marcobrianza/WeMakeColorsII/Arduino/WeMakeColorsII/app_status.h

#include "LED.h"

int const APP_START = 0;
int const UPDATE = 1;
int const AUTO_UPDATE = 2;
int const UPDATE_ERROR = -3;
int const UPDATE_OK = 3;
int const WIFI_MANAGER_AP = 4;
int const WIFI_MANAGER_SAVE = 5;


void showState(int s) {
  rgbColor_t c;
  //String ss;
  switch (s) {
    case UPDATE:
      c = { 64, 0, 0};
      break;
    case AUTO_UPDATE:
      c = {64, 0, 0};
      blink(10);
      break;
    case UPDATE_OK:
      c = {0, 64, 0};
      blink(10);
      break;
    case UPDATE_ERROR:
      c = {64, 64, 0};
      break;
    case WIFI_MANAGER_AP:
      //ss = "wifi manager ap";
      c =  {0, 0, 255};
      break;
    case WIFI_MANAGER_SAVE:
      c =  {0, 255, 255};
      break;
    case APP_START:
      //ss = "app start";
      c =  {255, 255, 255};
      break;

  }
  //if (ss != "") Serial.println(ss);
  showAllLeds(c);
}
